0x007E/tmp/TMP.asc

R1: EuropeanResistor; 6k52
R2: EuropeanResistor; {R}
R3: EuropeanResistor; 4k
R4: EuropeanResistor; 1k
Rop1: EuropeanResistor; 33k
Rop2: EuropeanResistor; 82k
U1: OP07
V1: voltage; 5
Named nets: V_IN, 0, V_OUT, VCC
.step param R 1630 3392 10
.op
